h2dakhil/Gym-Rep-Tracker/Firmware/src/main.h

#ifndef __MAIN_H
#define __MAIN_H

#ifdef __cplusplus
extern "C" {
#endif

#include "stm32f1xx_hal.h"

// Exported functions
void Error_Handler(void);

#ifdef __cplusplus
}
#endif

#endif /* __MAIN_H */
